Aaron-Mok/StereoCamera/CAD/Raspberry Pi HQ Camera Case - 4420496/images/back-cover.png

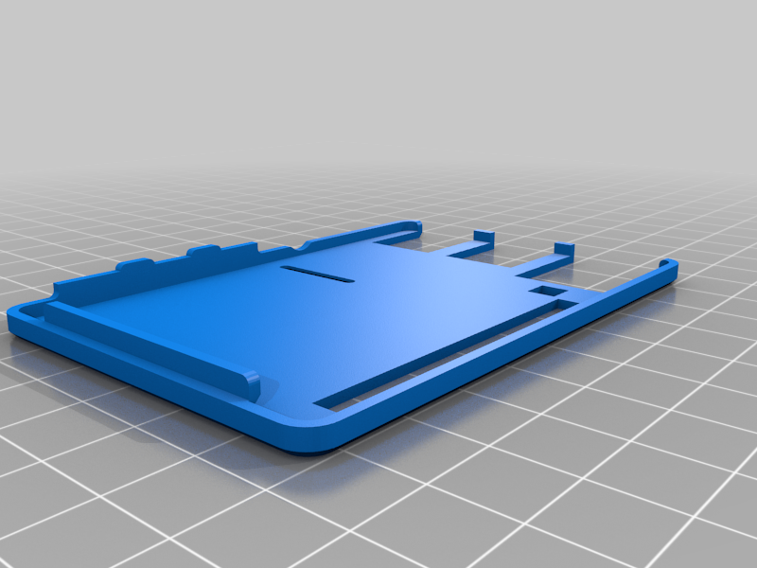
CAD/Raspberry Pi HQ Camera Case - 4420496/images/back-cover.png
