Aaron-Mok/StereoCamera/CAD/Raspberry Pi HQ Camera Case - 4420496/images/back-frame.png

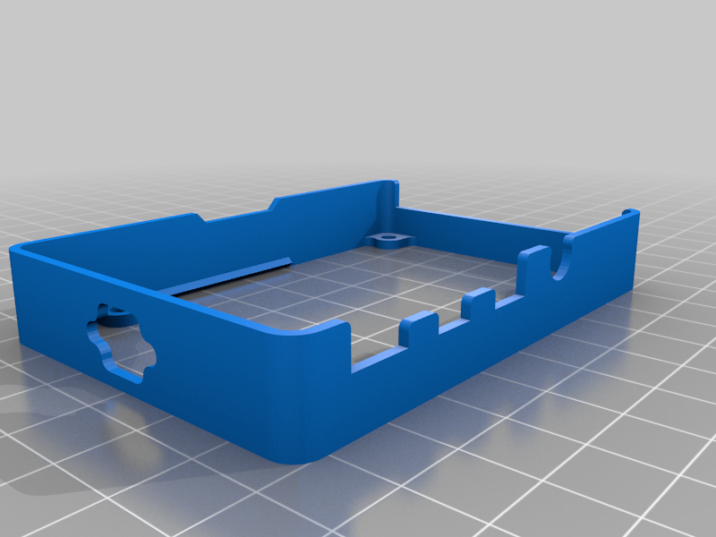
CAD/Raspberry Pi HQ Camera Case - 4420496/images/back-frame.png
