Aaron-Mok/StereoCamera/CAD/Raspberry Pi HQ Camera Case - 4420496/images/hero-camera.jpg

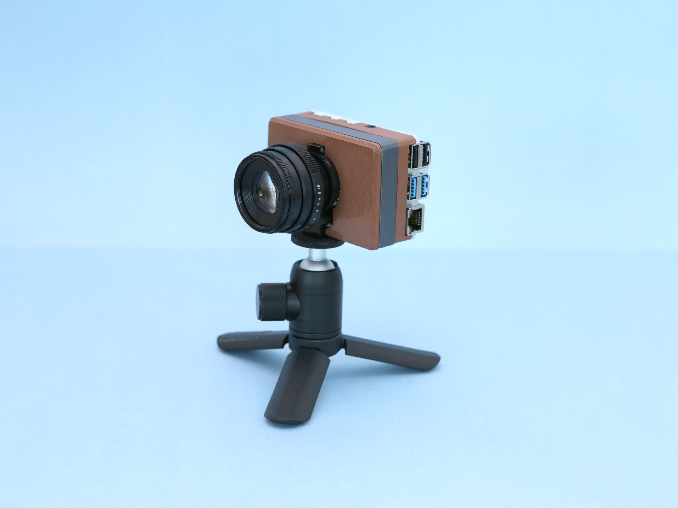
CAD/Raspberry Pi HQ Camera Case - 4420496/images/hero-camera.jpg
