Aaron-Mok/StereoCamera/CAD/Raspberry Pi HQ Camera Case - 4420496/images/pcb-mount.png

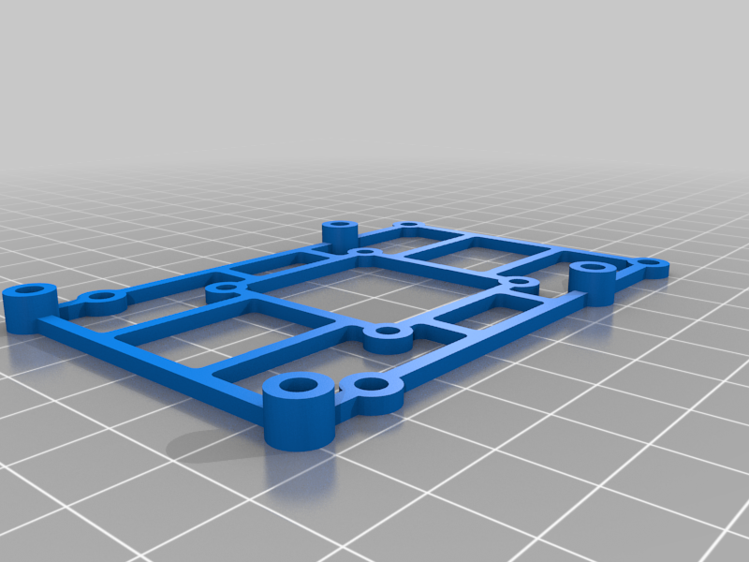
CAD/Raspberry Pi HQ Camera Case - 4420496/images/pcb-mount.png
