Aaron-Mok/StereoCamera/captures/bgr_image_awb_gamma_u801.png

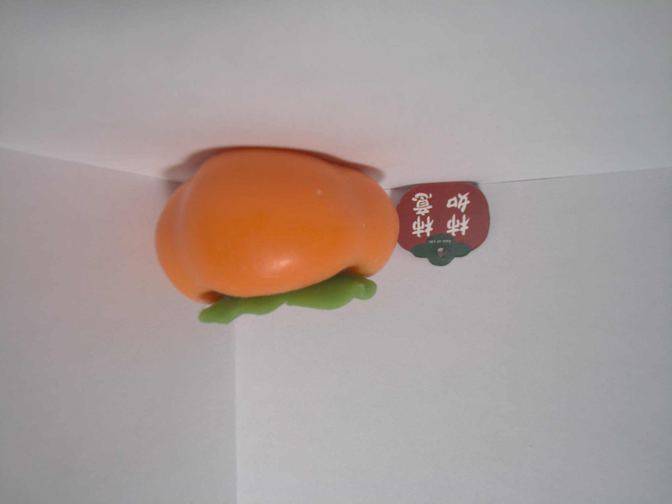
captures/bgr_image_awb_gamma_u801.png
