Aaron-Mok/StereoCamera/captures/depth_1781497462187.png

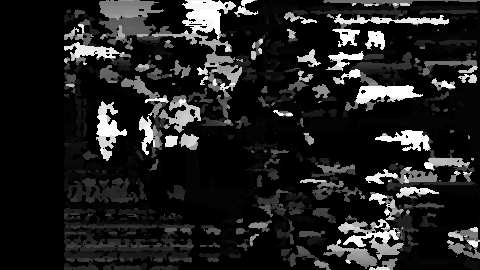
captures/depth_1781497462187.png
