Aaron-Mok/StereoCamera/captures/depth_1781998878519.png

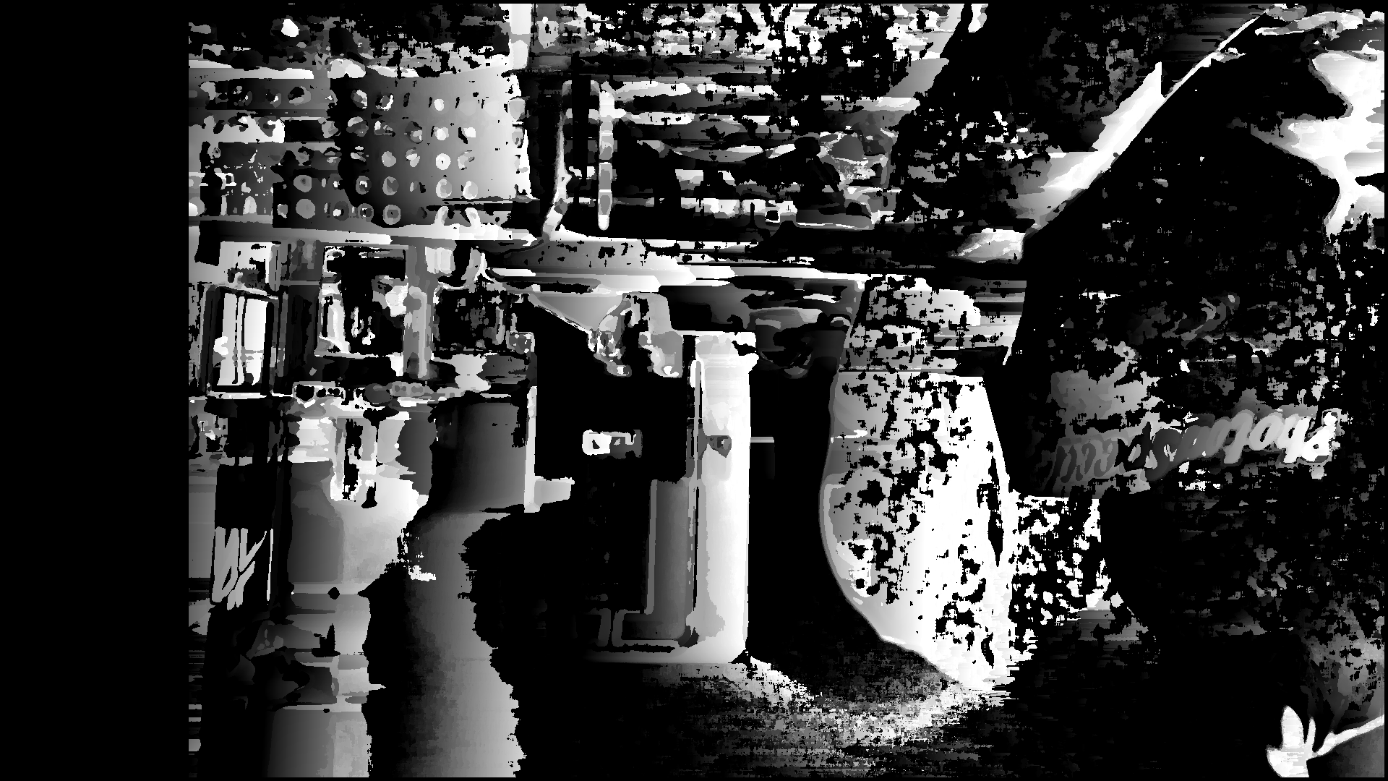
captures/depth_1781998878519.png
