Aaron-Mok/StereoCamera/captures/raw_u16_01.png

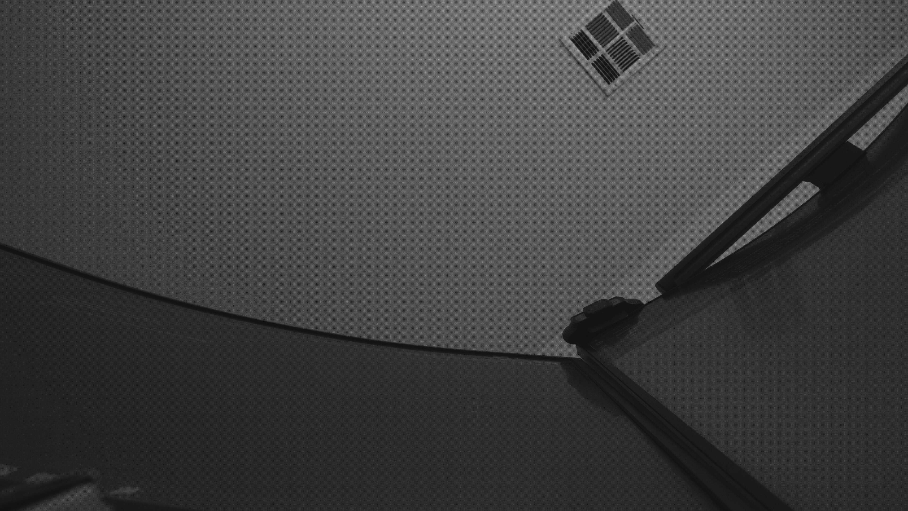
captures/raw_u16_01.png
