Aaron-Mok/StereoCamera/captures/rectL_1781497462187.png

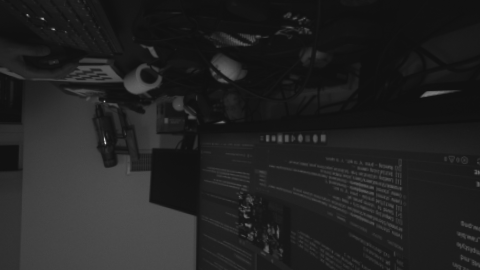
captures/rectL_1781497462187.png
