Aaron-Mok/StereoCamera/captures/rectL_1781998878519.png

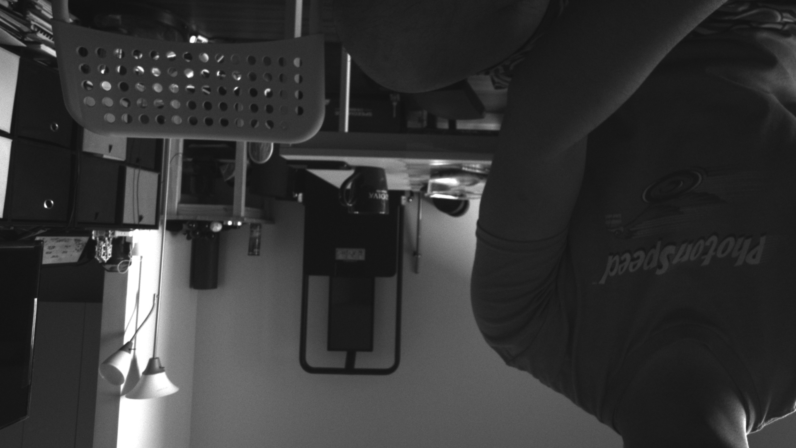
captures/rectL_1781998878519.png
