Aaron-Mok/StereoCamera/captures/rectR_1781497462187.png

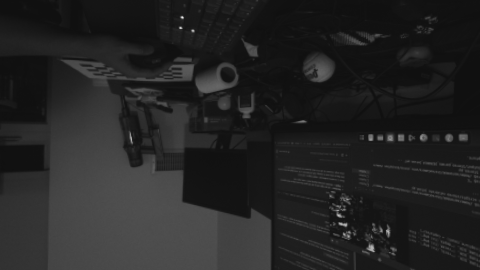
captures/rectR_1781497462187.png
