Aaron-Mok/StereoCamera/captures/rectR_1781998878519.png

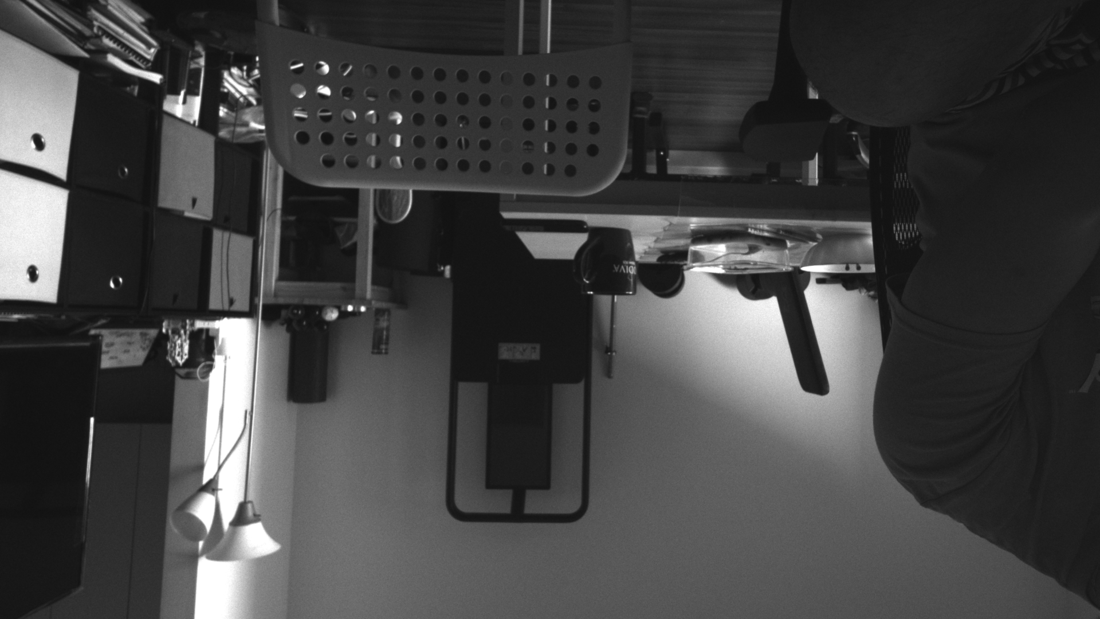
captures/rectR_1781998878519.png
