Aaron-Mok/StereoCamera/captures/white_balanced_image.png

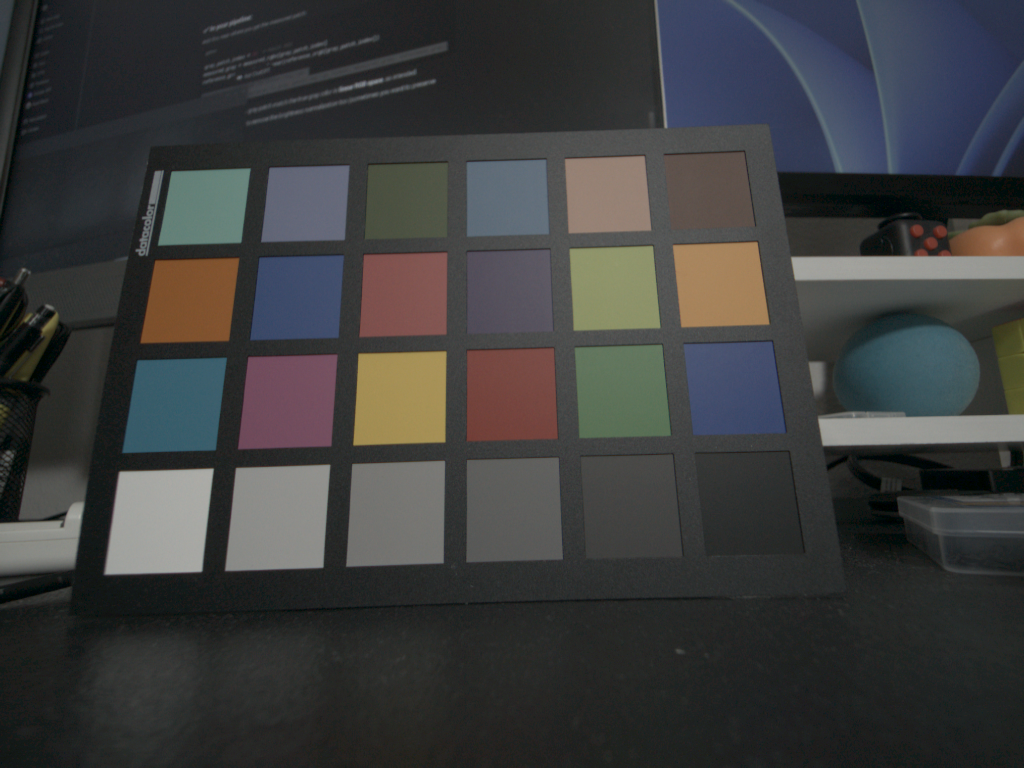
captures/white_balanced_image.png
