Aaron-Mok/StereoCamera/stereo_calib_pairs/left_1781990944117.png

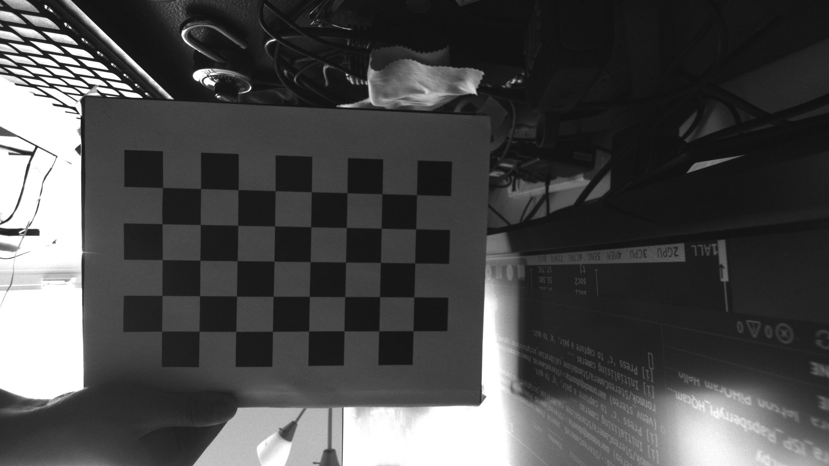
stereo_calib_pairs/left_1781990944117.png
