Aaron-Mok/StereoCamera/stereo_calib_pairs/left_1781990951715.png

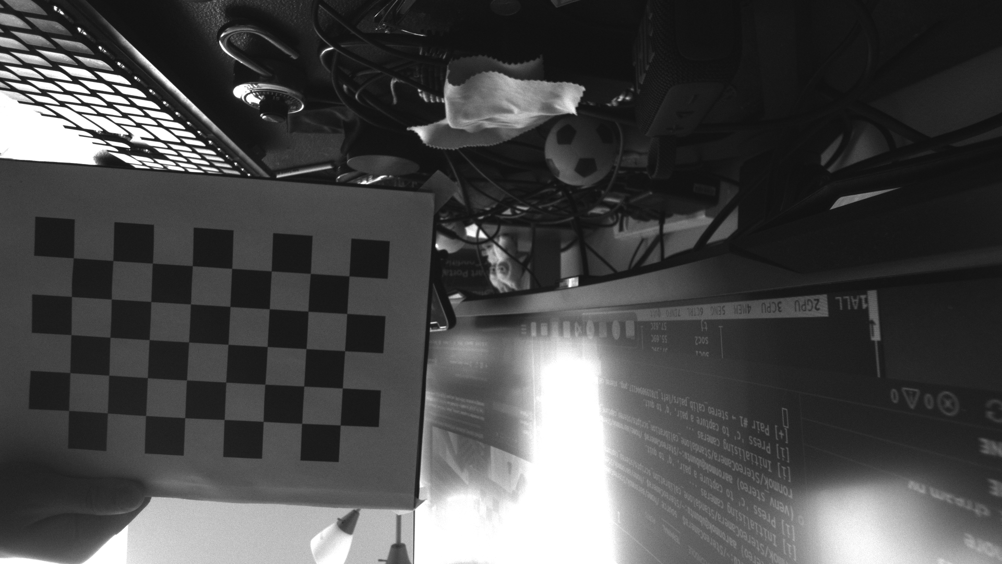
stereo_calib_pairs/left_1781990951715.png
