Aaron-Mok/StereoCamera/stereo_calib_pairs/left_1781990956050.png

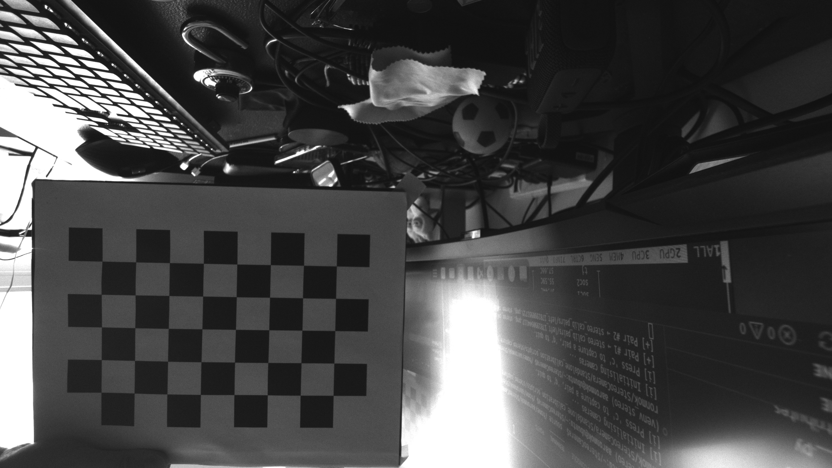
stereo_calib_pairs/left_1781990956050.png
