Aaron-Mok/StereoCamera/stereo_calib_pairs/left_1781990961881.png

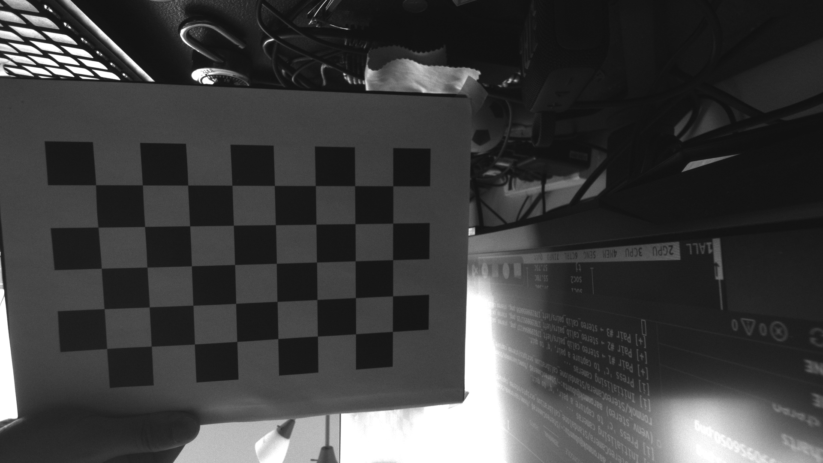
stereo_calib_pairs/left_1781990961881.png
