Aaron-Mok/StereoCamera/stereo_calib_pairs/left_1781990971266.png

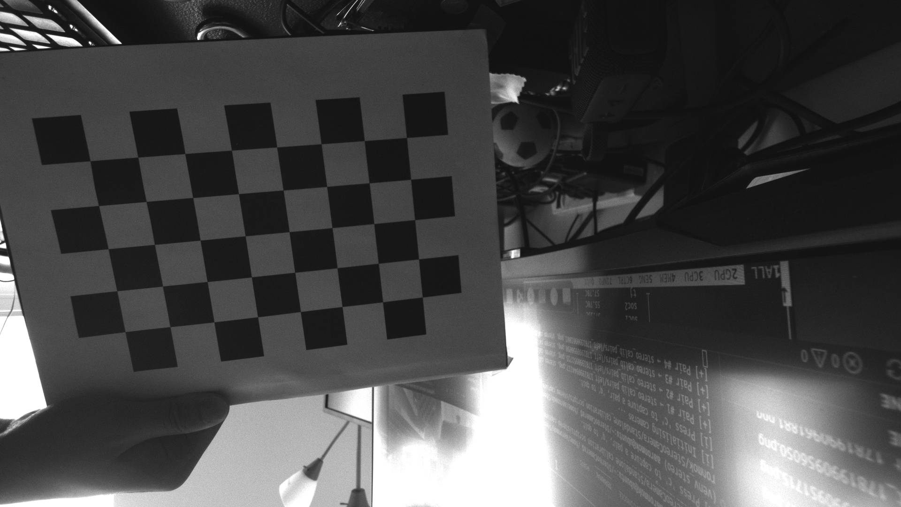
stereo_calib_pairs/left_1781990971266.png
