Aaron-Mok/StereoCamera/stereo_calib_pairs/left_1781990977469.png

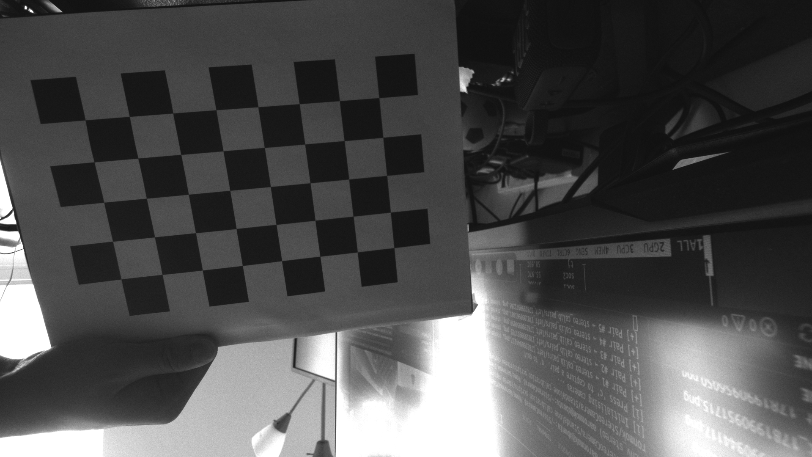
stereo_calib_pairs/left_1781990977469.png
