Aaron-Mok/StereoCamera/stereo_calib_pairs/left_1781991415851.png

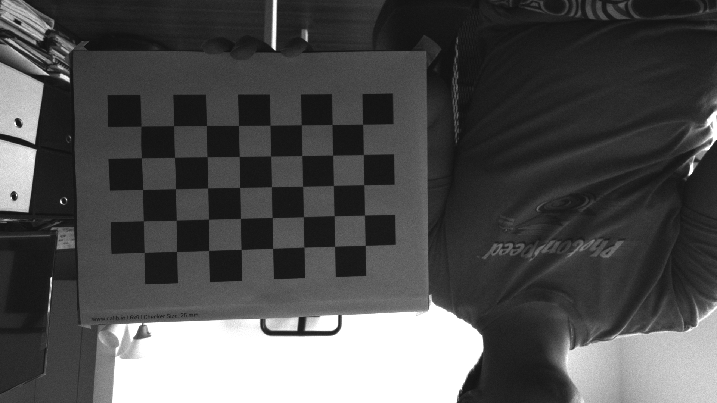
stereo_calib_pairs/left_1781991415851.png
