Aaron-Mok/StereoCamera/stereo_calib_pairs/left_1781996202573.png

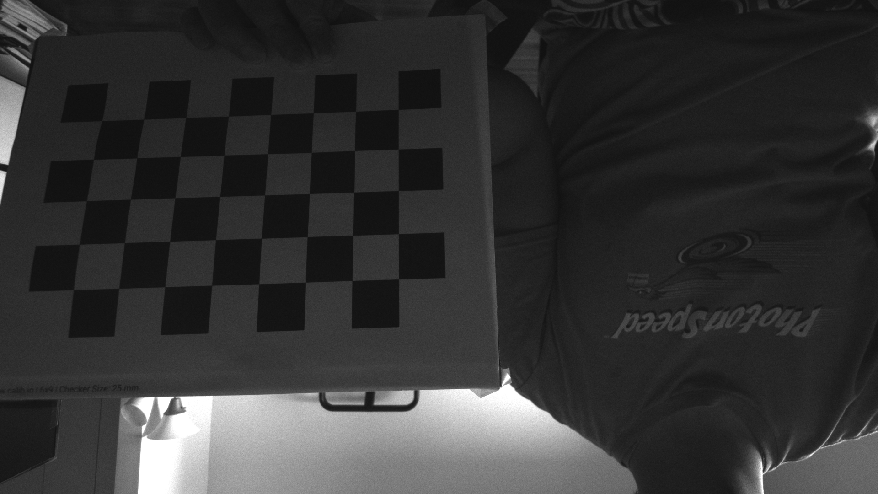
stereo_calib_pairs/left_1781996202573.png
