Aaron-Mok/StereoCamera/stereo_calib_pairs/left_1781996810830.png

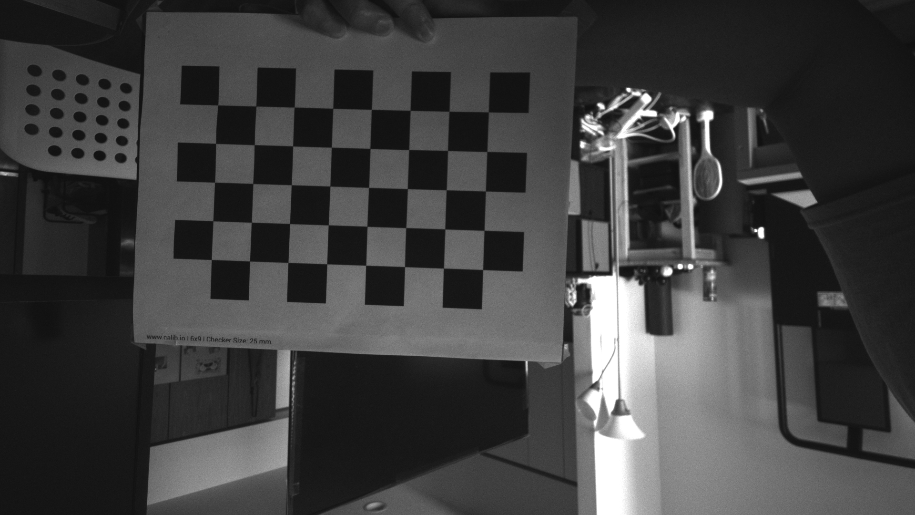
stereo_calib_pairs/left_1781996810830.png
