Aaron-Mok/StereoCamera/stereo_calib_pairs/left_1781996816100.png

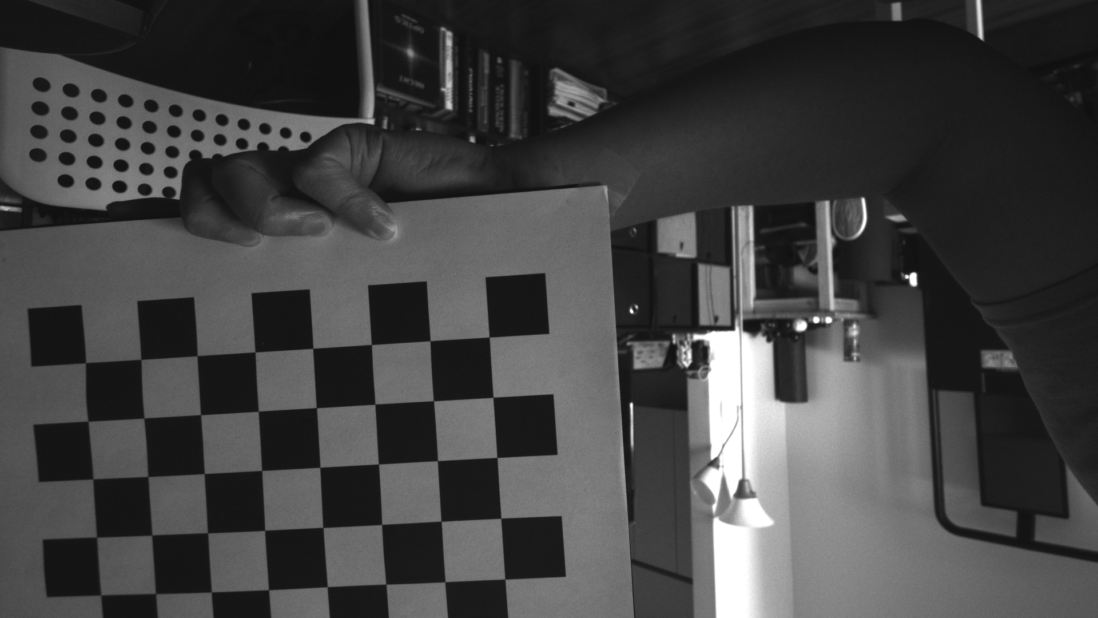
stereo_calib_pairs/left_1781996816100.png
