Aaron-Mok/StereoCamera/stereo_calib_pairs/left_1781996898139.png

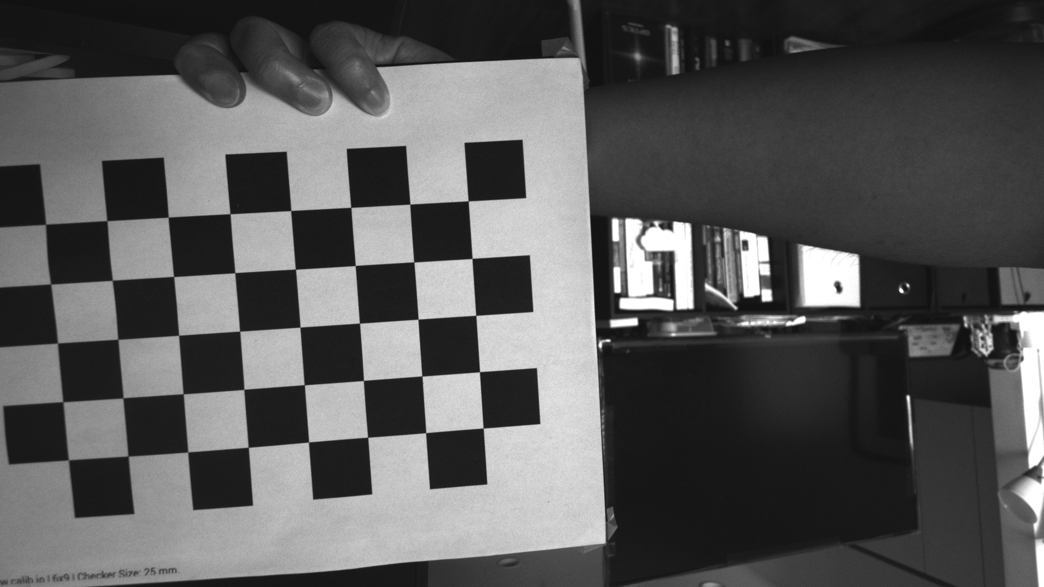
stereo_calib_pairs/left_1781996898139.png
