Aaron-Mok/StereoCamera/stereo_calib_pairs/left_1781996904151.png

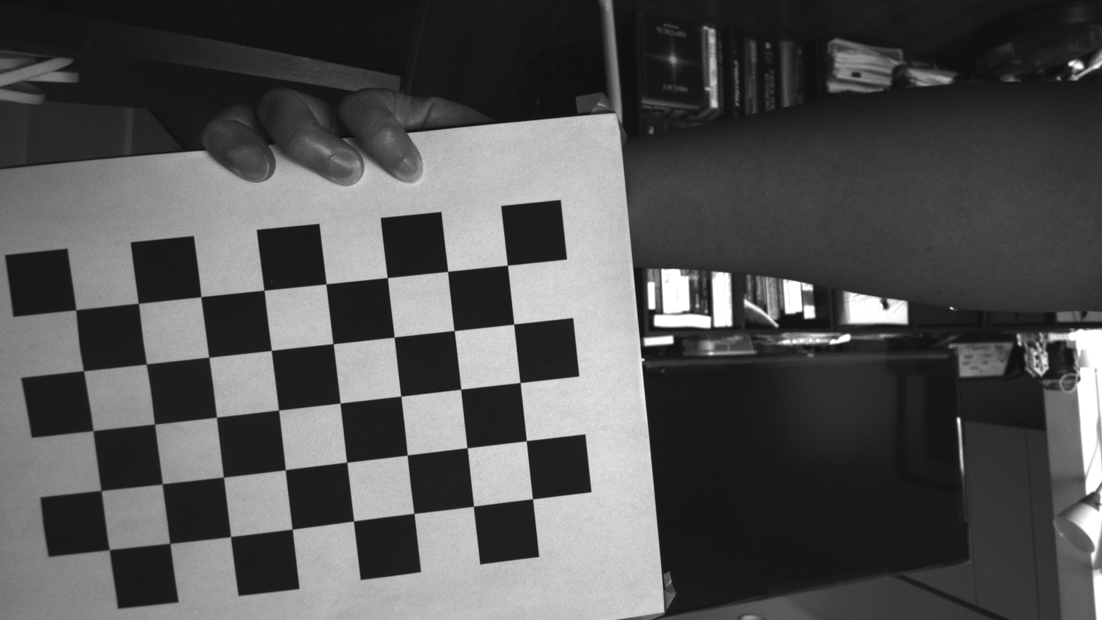
stereo_calib_pairs/left_1781996904151.png
