Aaron-Mok/StereoCamera/stereo_calib_pairs/left_1781996920679.png

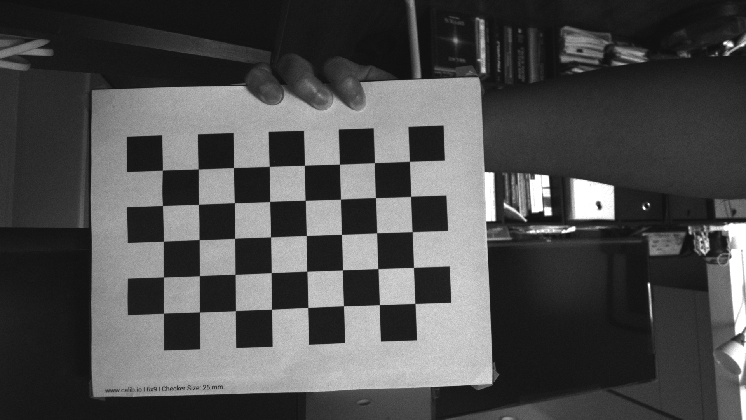
stereo_calib_pairs/left_1781996920679.png
