Aaron-Mok/StereoCamera/stereo_calib_pairs/left_1781996940578.png

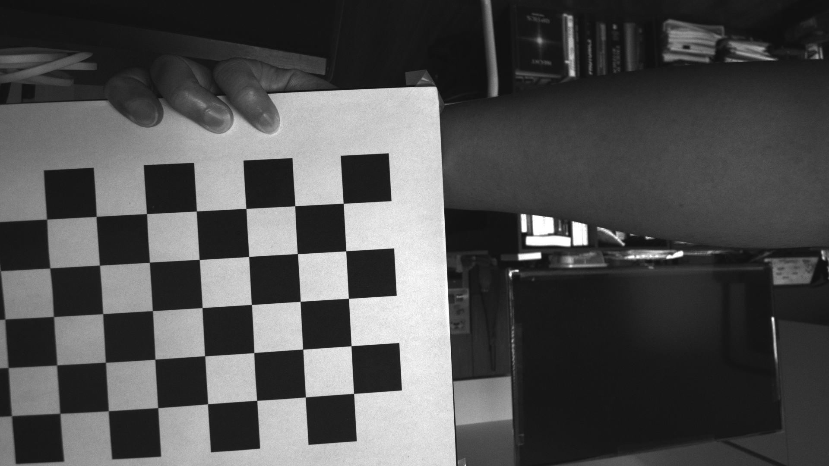
stereo_calib_pairs/left_1781996940578.png
