Aaron-Mok/StereoCamera/stereo_calib_pairs/right_1781990944117.png

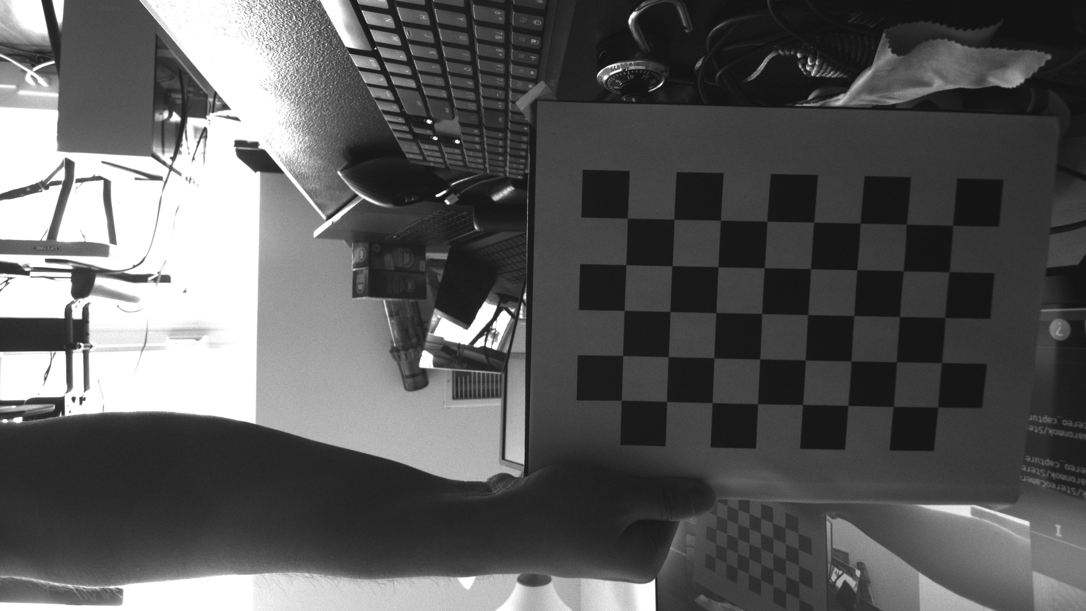
stereo_calib_pairs/right_1781990944117.png
