Aaron-Mok/StereoCamera/stereo_calib_pairs/right_1781990956050.png

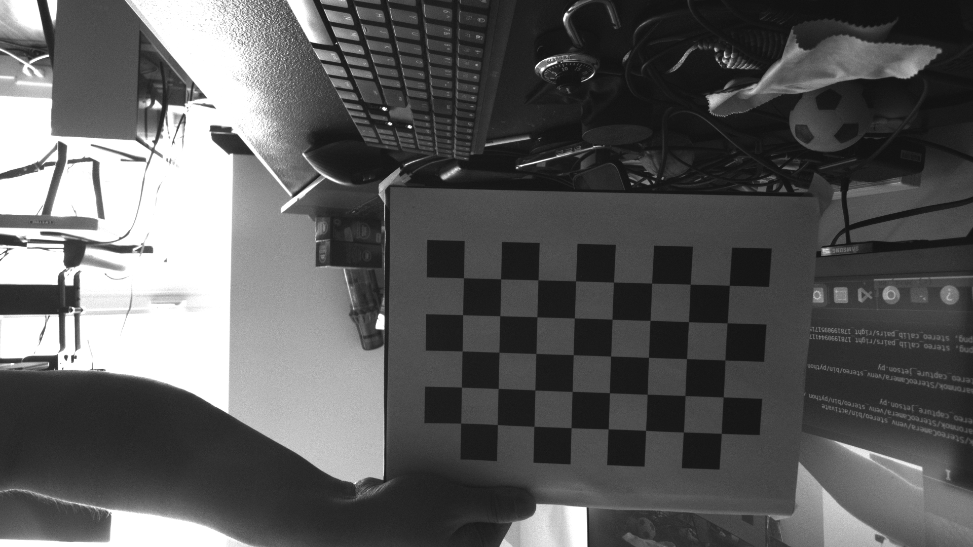
stereo_calib_pairs/right_1781990956050.png
