Aaron-Mok/StereoCamera/stereo_calib_pairs/right_1781990961881.png

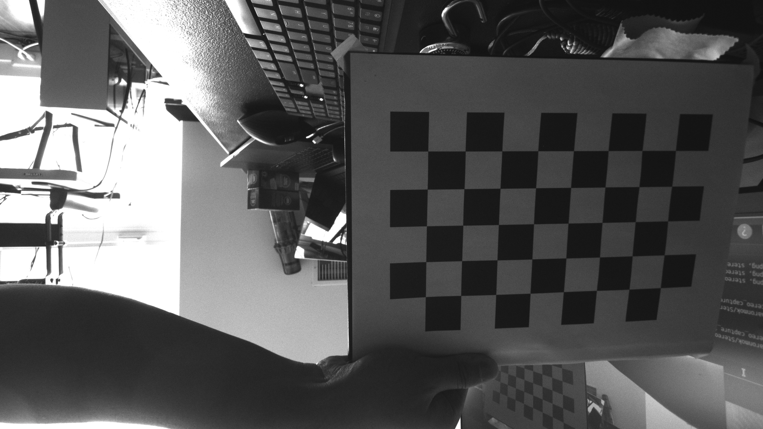
stereo_calib_pairs/right_1781990961881.png
