Aaron-Mok/StereoCamera/stereo_calib_pairs/right_1781990977469.png

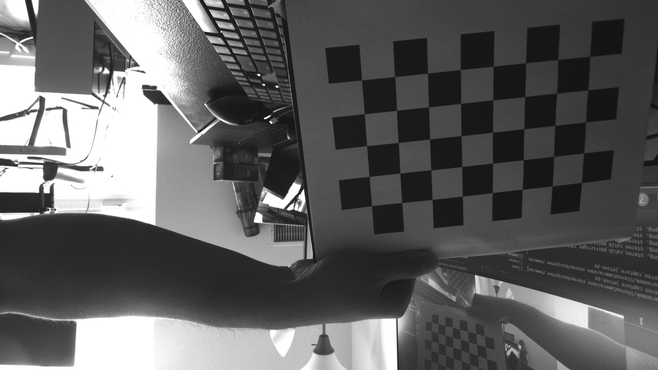
stereo_calib_pairs/right_1781990977469.png
