Aaron-Mok/StereoCamera/stereo_calib_pairs/right_1781996202573.png

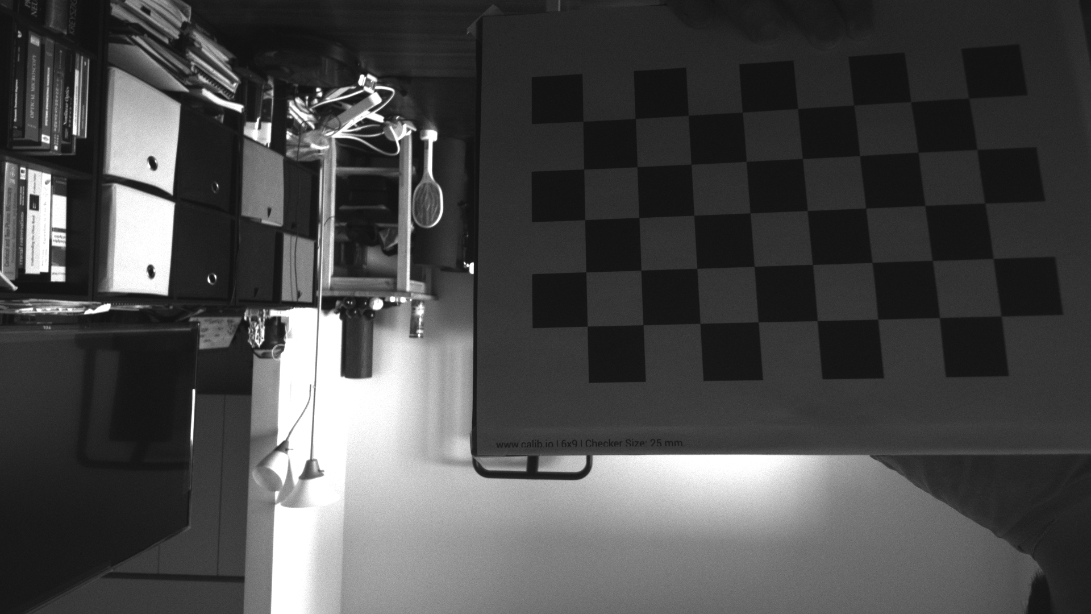
stereo_calib_pairs/right_1781996202573.png
