Aaron-Mok/StereoCamera/stereo_calib_pairs/right_1781996804988.png

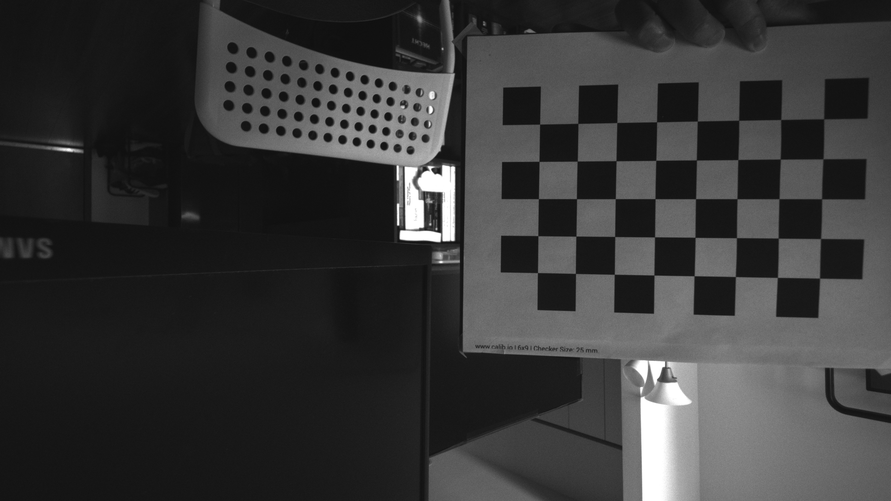
stereo_calib_pairs/right_1781996804988.png
