Aaron-Mok/StereoCamera/stereo_calib_pairs/right_1781996810830.png

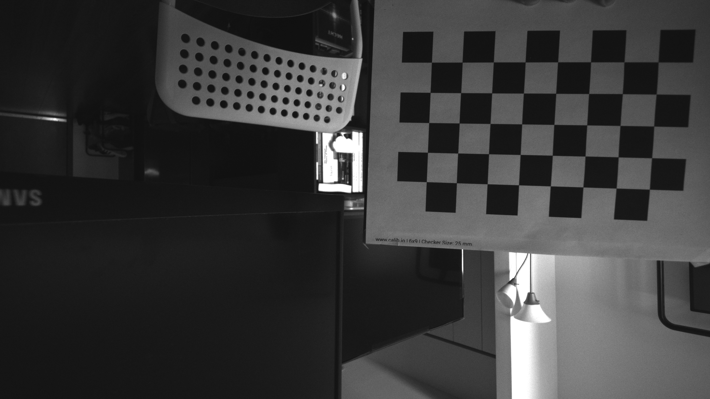
stereo_calib_pairs/right_1781996810830.png
