Aaron-Mok/StereoCamera/stereo_calib_pairs/right_1781996816100.png

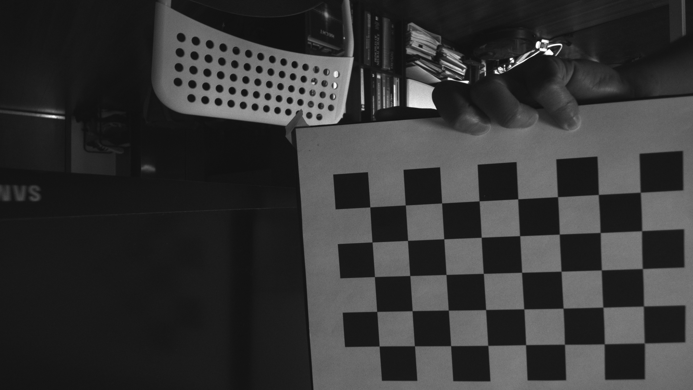
stereo_calib_pairs/right_1781996816100.png
