Aaron-Mok/StereoCamera/stereo_calib_pairs/right_1781996898139.png

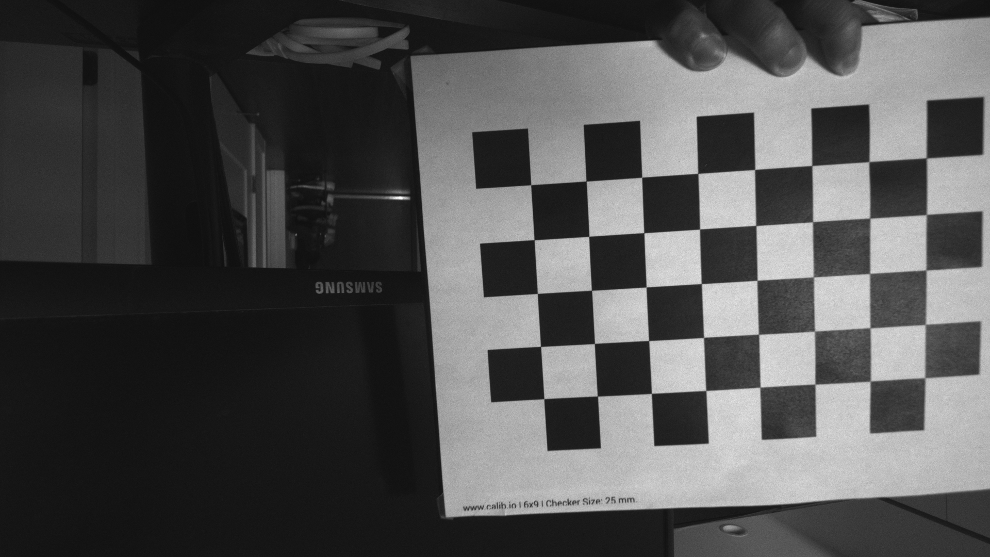
stereo_calib_pairs/right_1781996898139.png
