Aaron-Mok/StereoCamera/stereo_calib_pairs/right_1781996904151.png

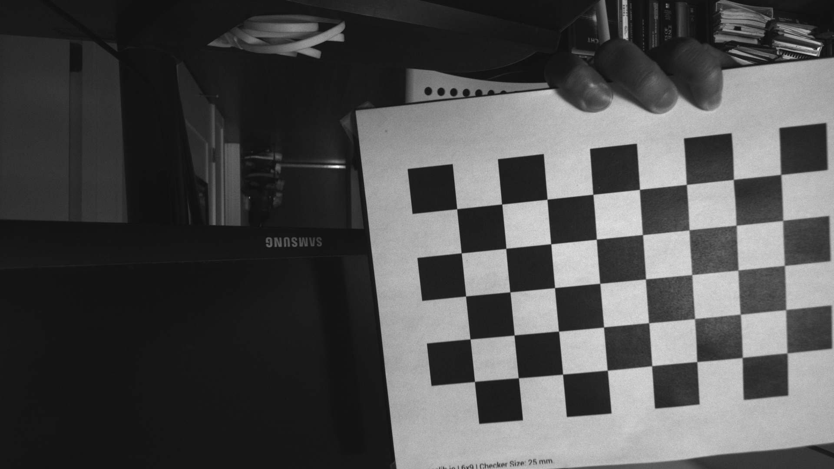
stereo_calib_pairs/right_1781996904151.png
