Aaron-Mok/StereoCamera/stereo_calib_pairs/right_1781996910558.png

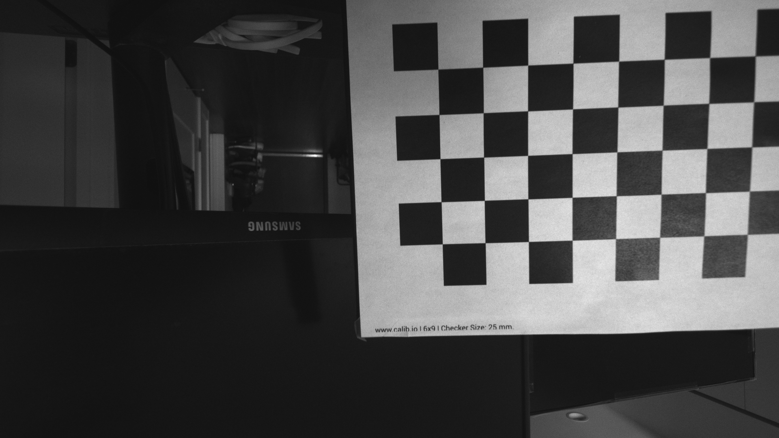
stereo_calib_pairs/right_1781996910558.png
