Aaron-Mok/StereoCamera/stereo_calib_pairs/right_1781996920679.png

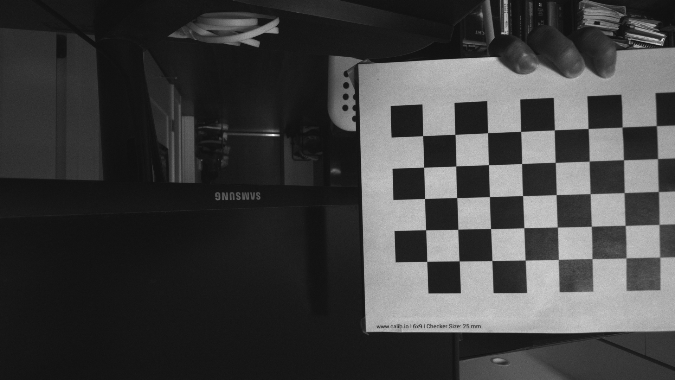
stereo_calib_pairs/right_1781996920679.png
