Aaron-Mok/StereoCamera/stereo_calib_pairs/right_1781996940578.png

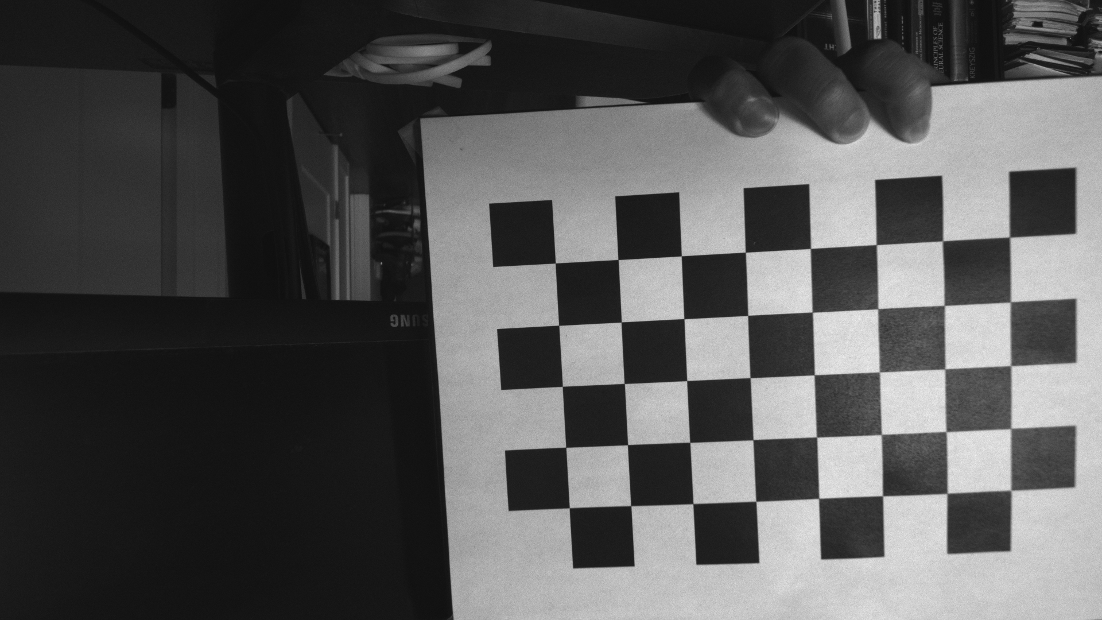
stereo_calib_pairs/right_1781996940578.png
