Aaron-Mok/StereoCamera/window.png

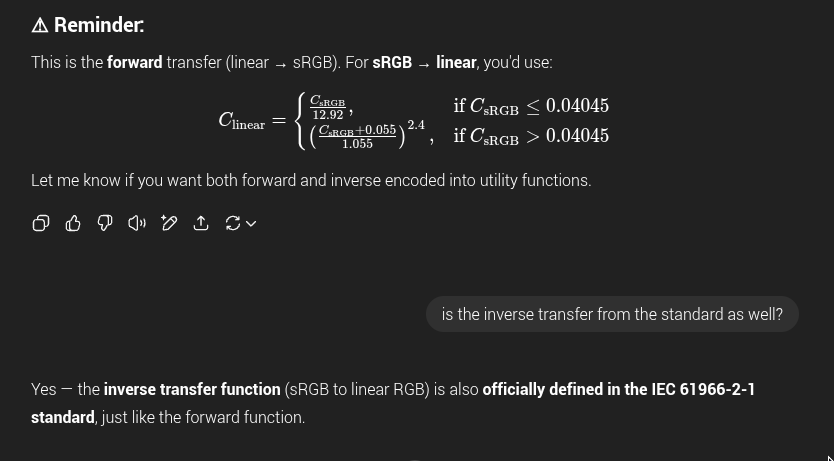
window.png
