Aaron-Mok/StereoCamera/Calibration_output/black_offset_script_check_lens_cover_open.png

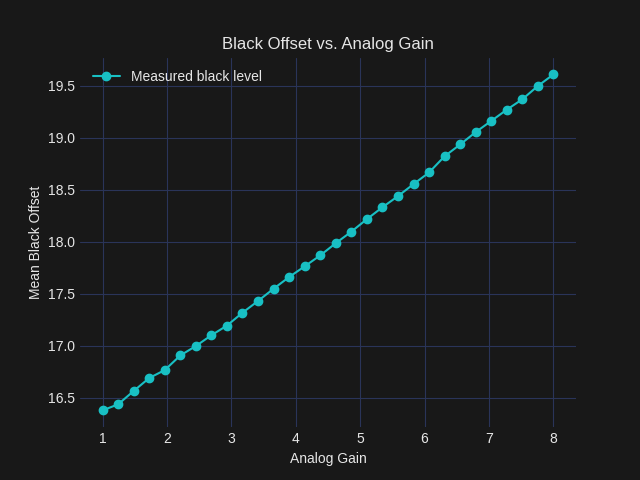
Calibration_output/black_offset_script_check_lens_cover_open.png
