Aaron-Mok/StereoCamera/stereo_calib_pairs/debug_corners/pair015_L.jpg

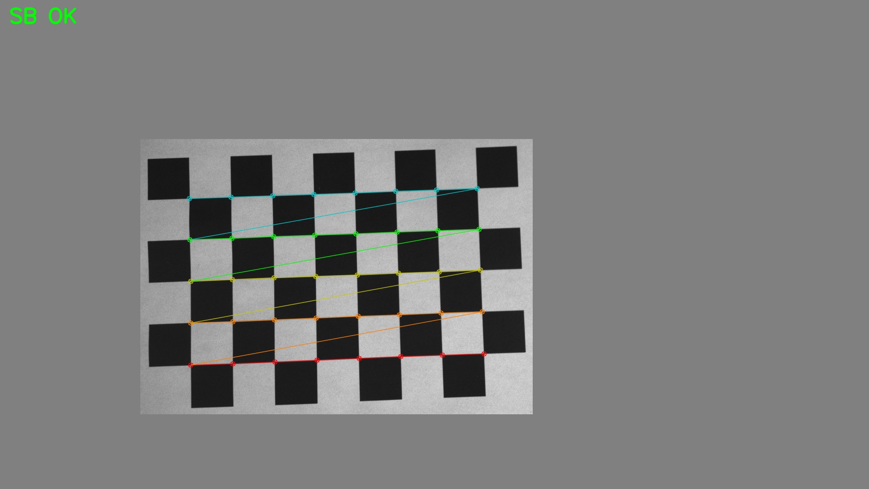
stereo_calib_pairs/debug_corners/pair015_L.jpg
