Aaron-Mok/StereoCamera/stereo_calib_pairs/debug_corners/pair016_L.jpg

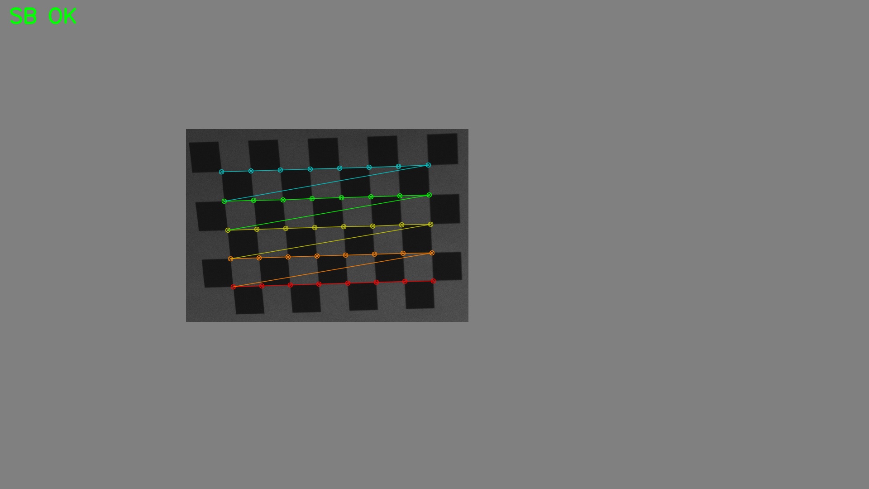
stereo_calib_pairs/debug_corners/pair016_L.jpg
