Aaron-Mok/StereoCamera/stereo_calib_pairs/debug_corners/pair018_L.jpg

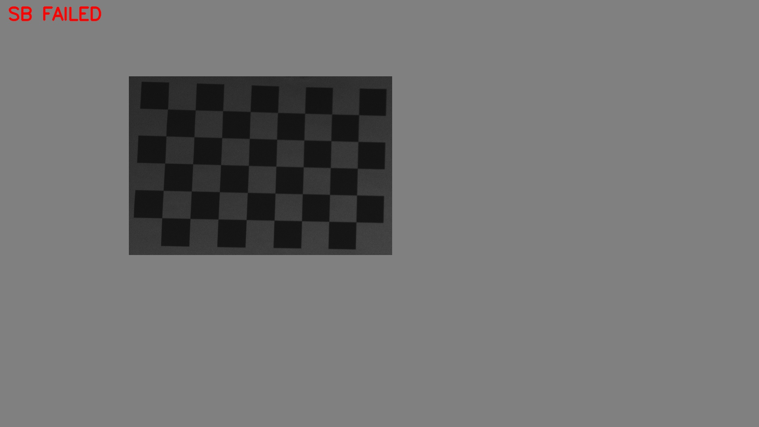
stereo_calib_pairs/debug_corners/pair018_L.jpg
