Aaron-Mok/StereoCamera/stereo_calib_pairs/debug_corners/pair019_R.jpg

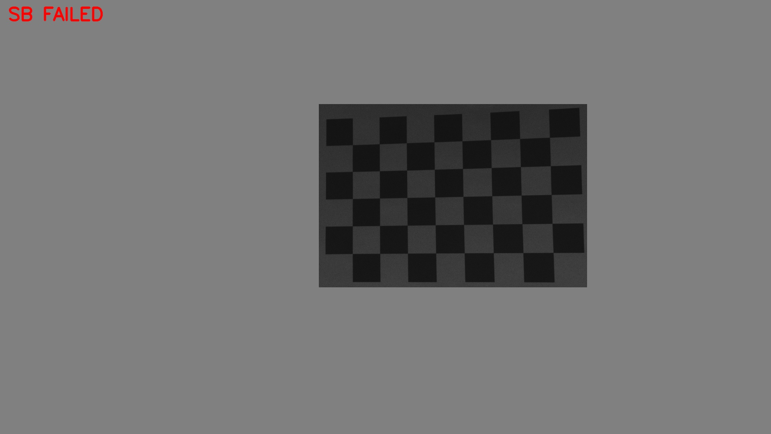
stereo_calib_pairs/debug_corners/pair019_R.jpg
