Aaron-Mok/StereoCamera/argus_stream.py

import cv2
import sys

def gstreamer_pipeline(width=1920, height=1080, fps=30, flip=0):
    return (
        f"nvarguscamerasrc ! "
        f"video/x-raw(memory:NVMM), width={width}, height={height}, framerate={fps}/1 ! "
        f"nvvidconv flip-method={flip} ! "
        f"video/x-raw, format=BGRx ! "
        f"videoconvert ! "
        f"video/x-raw, format=BGR ! "
        f"appsink drop=1"
    )

pipeline = gstreamer_pipeline()
print(f"Pipeline: {pipeline}")

cap = cv2.VideoCapture(pipeline, cv2.CAP_GSTREAMER)

if not cap.isOpened():
    print("ERROR: Could not open camera via nvarguscamerasrc.")
    print("Check that the Argus daemon is running and the camera is connected.")
    sys.exit(1)

print("Camera opened successfully. Press 'q' to quit.")

while True:
    ret, frame = cap.read()
    if not ret:
        print("ERROR: Failed to grab frame.")
        break

    h, w = frame.shape[:2]
    cv2.putText(frame, f"{w}x{h}", (20, 40), cv2.FONT_HERSHEY_SIMPLEX, 1, (0, 255, 0), 2)
    cv2.imshow("Argus Stream", frame)

    if cv2.waitKey(1) & 0xFF == ord('q'):
        break

cap.release()
cv2.destroyAllWindows()
