Aaron-Mok/StereoCamera/Standalone_calibration_scripts/stereo_calibrate_live_jetson.py

#!/usr/bin/env python3
"""
Stereo calibration script for dual Pi HQ cameras on Jetson Nano.
Cameras are read as raw Bayer uint16 via v4l2-ctl; green channel is
extracted for calibration since it has the most pixels and sharpest detail.

Controls:
  c  - capture a pair (only works when both cameras detect the checkerboard)
  s  - run stereo calibration with collected pairs
  q  - quit without calibrating

TODO: This is trying to use findChessboardCOrnerSB, which does not seems to work.
Can switch back to findChessboardCorners if needed, but SB is supposed to be more robust and accurate. 
"""
import sys
import os
sys.path.insert(0, os.path.abspath(os.path.join(os.path.dirname(__file__), "..")))

import cv2
import numpy as np
import time

from ISP.binning import extract_green, bin_2x2
from camera_utils import initialize_camera_jetson, capture_raw_frame_jetson
from conversion_utils import bit16_to_bit8

# ─── Settings ──────────────────────────────────────────────────────────────────
LEFT_DEVICE  = "/dev/video0"
RIGHT_DEVICE = "/dev/video1"

W, H         = 3840, 2160          # sensor resolution
EXPOSURE     = 33000
GAIN         = 200
FRAME_RATE   = 30000000

# extract_green → (H//2, W//2), then bin_2x2 → (H//4, W//4) = (540, 960)
IMG_W, IMG_H = W // 4, H // 4

# Checkerboard inner-corner count (not number of squares)
CB_COLS       = 8
CB_ROWS       = 5
SQUARE_SIZE_M = 0.025              # square side length in metres

MIN_PAIRS = 15

OUT_DIR  = "stereo_calib_pairs"
YAML_OUT = "stereo_params.yml"

# ───────────────────────────────────────────────────────────────────────────────


def raw_to_gray8(raw_u16: np.ndarray) -> np.ndarray:
    """Extract green channel, 2×2 bin to 960×540, convert to uint8."""
    return bit16_to_bit8(bin_2x2(extract_green(raw_u16)))


def find_corners(gray, pattern_size):
    """Detect directly at 960×540. SB includes subpixel — no further scaling needed."""
    sb_flags = cv2.CALIB_CB_NORMALIZE_IMAGE
    return cv2.findChessboardCornersSB(gray, pattern_size, sb_flags)


def make_object_points(pattern_size, square_size_m):
    cb_cols, cb_rows = pattern_size
    objp = np.zeros((cb_rows * cb_cols, 3), np.float32)
    objp[:, :2] = np.mgrid[0:cb_cols, 0:cb_rows].T.reshape(-1, 2)
    objp *= square_size_m
    return objp


def save_yaml(filepath, data_dict):
    fs = cv2.FileStorage(filepath, cv2.FILE_STORAGE_WRITE)
    for k, v in data_dict.items():
        fs.write(k, v)
    fs.release()


def main():
    os.makedirs(OUT_DIR, exist_ok=True)

    print("[i] Initialising left camera  ...")
    pL, _ = initialize_camera_jetson(LEFT_DEVICE,  W, H, EXPOSURE, GAIN, FRAME_RATE)
    print("[i] Initialising right camera ...")
    pR, _ = initialize_camera_jetson(RIGHT_DEVICE, W, H, EXPOSURE, GAIN, FRAME_RATE)

    pattern_size = (CB_COLS, CB_ROWS)
    objp = make_object_points(pattern_size, SQUARE_SIZE_M)
    image_size   = (IMG_W, IMG_H)   # (width, height) as OpenCV expects

    objpoints  = []
    imgpointsL = []
    imgpointsR = []
    pair_count = 0

    font = cv2.FONT_HERSHEY_SIMPLEX

    print("[i] Press 'c' to capture a pair when both detections are green.")
    print(f"[i] Press 's' to run calibration (need at least {MIN_PAIRS} pairs).")
    print("[i] Press 'q' to quit.")

    while True:
        raw_L = capture_raw_frame_jetson(pL, W, H)
        raw_R = capture_raw_frame_jetson(pR, W, H)
        if raw_L is None or raw_R is None:
            print("[!] Frame grab failed — exiting.")
            break

        grayL = raw_to_gray8(raw_L)
        grayR = raw_to_gray8(raw_R)

        foundL, cornersL = find_corners(grayL, pattern_size)
        foundR, cornersR = find_corners(grayR, pattern_size)

        # 960×540 is directly displayable — no resize needed
        showL = grayL.copy()
        showR = grayR.copy()

        if foundL:
            cv2.drawChessboardCorners(showL, pattern_size, cornersL, foundL)
        if foundR:
            cv2.drawChessboardCorners(showR, pattern_size, cornersR, foundR)

        colorL = (0, 200, 0) if foundL else (0, 0, 255)
        colorR = (0, 200, 0) if foundR else (0, 0, 255)
        cv2.putText(showL, f"Left:  {'OK' if foundL else 'NO'}",  (20, 40),  font, 1.0, colorL, 2, cv2.LINE_AA)
        cv2.putText(showR, f"Right: {'OK' if foundR else 'NO'}", (20, 40),  font, 1.0, colorR, 2, cv2.LINE_AA)
        cv2.putText(showL, f"Pairs: {pair_count}",               (20, 80),  font, 0.8, (255, 255, 255), 2, cv2.LINE_AA)
        cv2.putText(showR, f"c=capture  s=calibrate  q=quit",    (20, 80),  font, 0.8, (255, 255, 255), 2, cv2.LINE_AA)

        cv2.imshow("Left", showL)
        cv2.imshow("Right", showR)

        key = cv2.waitKey(1) & 0xFF

        if key == ord('q'):
            print("[i] Quit — no calibration saved.")
            break

        elif key == ord('c'):
            if foundL and foundR:
                ts = int(time.time() * 1000)
                lp = os.path.join(OUT_DIR, f"left_{ts}.png")
                rp = os.path.join(OUT_DIR, f"right_{ts}.png")
                cv2.imwrite(lp, grayL)
                cv2.imwrite(rp, grayR)
                objpoints.append(objp.copy())
                imgpointsL.append(cornersL)
                imgpointsR.append(cornersR)
                pair_count += 1
                print(f"[+] Pair #{pair_count} saved → {lp}, {rp}")
            else:
                print("[!] Skipped — need checkerboard visible in BOTH cameras.")

        elif key == ord('s'):
            if pair_count < MIN_PAIRS:
                print(f"[!] Need at least {MIN_PAIRS} pairs; have {pair_count}.")
                continue

            print("[i] Running per-camera calibration ...")
            retL, K1, D1, _, _ = cv2.calibrateCamera(objpoints, imgpointsL, image_size, None, None)
            retR, K2, D2, _, _ = cv2.calibrateCamera(objpoints, imgpointsR, image_size, None, None)
            print(f"[i] RMS  left={retL:.4f}  right={retR:.4f}")

            sc_flags = (cv2.CALIB_USE_INTRINSIC_GUESS |
                        cv2.CALIB_RATIONAL_MODEL       |
                        cv2.CALIB_FIX_K3)
            if hasattr(cv2, "CALIB_FIX_TAUX_TAUY"):
                sc_flags |= cv2.CALIB_FIX_TAUX_TAUY

            sc_criteria = (cv2.TERM_CRITERIA_MAX_ITER + cv2.TERM_CRITERIA_EPS, 100, 1e-6)

            print("[i] Running stereoCalibrate ...")
            rms, K1, D1, K2, D2, R, T, E, F = cv2.stereoCalibrate(
                objpoints, imgpointsL, imgpointsR,
                K1, D1, K2, D2,
                image_size, criteria=sc_criteria, flags=sc_flags
            )
            print(f"[i] Stereo RMS : {rms:.4f}")
            print(f"[i] Baseline   : {np.linalg.norm(T)*100:.2f} cm")

            print("[i] Computing stereoRectify + remap tables ...")
            R1, R2, P1, P2, Q, roi1, roi2 = cv2.stereoRectify(
                K1, D1, K2, D2, image_size, R, T,
                flags=cv2.CALIB_ZERO_DISPARITY, alpha=0
            )
            map1x, map1y = cv2.initUndistortRectifyMap(K1, D1, R1, P1, image_size, cv2.CV_32FC1)
            map2x, map2y = cv2.initUndistortRectifyMap(K2, D2, R2, P2, image_size, cv2.CV_32FC1)

            out = {
                "image_width":  image_size[0],
                "image_height": image_size[1],
                "K1": K1, "D1": D1,
                "K2": K2, "D2": D2,
                "R":  R,  "T":  T,  "E": E, "F": F,
                "R1": R1, "R2": R2, "P1": P1, "P2": P2, "Q": Q,
                "roi1": np.array(roi1, dtype=np.int32),
                "roi2": np.array(roi2, dtype=np.int32),
                "map1x": map1x, "map1y": map1y,
                "map2x": map2x, "map2y": map2y,
                "square_size_m": float(SQUARE_SIZE_M),
                "cb_cols": int(CB_COLS),
                "cb_rows": int(CB_ROWS),
            }
            save_yaml(YAML_OUT, out)
            print(f"[✓] Saved to '{YAML_OUT}'")

            # ── Rectified live preview ──────────────────────────────────────
            print("[i] Rectified preview — press 'q' to exit.")
            gpu_map1x = cv2.cuda_GpuMat(); gpu_map1x.upload(map1x)
            gpu_map1y = cv2.cuda_GpuMat(); gpu_map1y.upload(map1y)
            gpu_map2x = cv2.cuda_GpuMat(); gpu_map2x.upload(map2x)
            gpu_map2y = cv2.cuda_GpuMat(); gpu_map2y.upload(map2y)

            while True:
                raw_L2 = capture_raw_frame_jetson(pL, W, H)
                raw_R2 = capture_raw_frame_jetson(pR, W, H)
                if raw_L2 is None or raw_R2 is None:
                    break
                gL2 = raw_to_gray8(raw_L2)
                gR2 = raw_to_gray8(raw_R2)

                gpu_gL2 = cv2.cuda_GpuMat(); gpu_gL2.upload(gL2)
                gpu_gR2 = cv2.cuda_GpuMat(); gpu_gR2.upload(gR2)
                gpu_rectL = cv2.cuda.remap(gpu_gL2, gpu_map1x, gpu_map1y, cv2.INTER_LINEAR)
                gpu_rectR = cv2.cuda.remap(gpu_gR2, gpu_map2x, gpu_map2y, cv2.INTER_LINEAR)

                # Resize to 960×540 on GPU, cvtColor, download for hconcat
                # 960×540 frames — cvtColor on GPU, hconcat on CPU → 1920×540
                bgrL = cv2.cuda.cvtColor(gpu_rectL, cv2.COLOR_GRAY2BGR).download()
                bgrR = cv2.cuda.cvtColor(gpu_rectR, cv2.COLOR_GRAY2BGR).download()
                both = cv2.hconcat([bgrL, bgrR])  # 1920×540 — directly displayable
                for y in range(0, both.shape[0], 60):
                    cv2.line(both, (0, y), (both.shape[1] - 1, y), (0, 255, 0), 1, cv2.LINE_AA)
                cv2.imshow("Rectified Preview (q to quit)", both)
                if cv2.waitKey(1) & 0xFF == ord('q'):
                    break
            break

    cv2.destroyAllWindows()
    pL.terminate()
    pR.terminate()


if __name__ == "__main__":
    main()
