Aaron-Mok/StereoCamera/Standalone_calibration_scripts/stereo_capture_jetson.py

#!/usr/bin/env python3
"""
Capture stereo image pairs for offline calibration.
Live preview at 960×540 for framing; saves full 1920×1080 green-channel images.

Controls:
  c - capture a pair
  q - quit
"""
import sys
import os
sys.path.insert(0, os.path.abspath(os.path.join(os.path.dirname(__file__), "..")))

import cv2
import numpy as np
import time

from ISP.binning import extract_green
from camera_utils import initialize_camera_jetson, capture_raw_frame_jetson
from conversion_utils import bit16_to_bit8

# ─── Settings ──────────────────────────────────────────────────────────────────
LEFT_DEVICE  = "/dev/video0"
RIGHT_DEVICE = "/dev/video1"

W, H       = 3840, 2160
EXPOSURE   = 33000
GAIN       = 200
FRAME_RATE = 30000000

OUT_DIR = "stereo_calib_pairs"
# ───────────────────────────────────────────────────────────────────────────────


def main():
    os.makedirs(OUT_DIR, exist_ok=True)

    print("[i] Initialising cameras ...")
    pL, _ = initialize_camera_jetson(LEFT_DEVICE,  W, H, EXPOSURE, GAIN, FRAME_RATE)
    pR, _ = initialize_camera_jetson(RIGHT_DEVICE, W, H, EXPOSURE, GAIN, FRAME_RATE)

    print("[i] Press 'c' to capture a pair, 'q' to quit.")
    pair_count = 0
    font = cv2.FONT_HERSHEY_SIMPLEX

    while True:
        raw_L = capture_raw_frame_jetson(pL, W, H)
        raw_R = capture_raw_frame_jetson(pR, W, H)
        if raw_L is None or raw_R is None:
            print("[!] Frame grab failed.")
            break

        # Full 1920×1080 green channel — saved on capture
        greenL = bit16_to_bit8(extract_green(raw_L))
        greenR = bit16_to_bit8(extract_green(raw_R))

        # Downscale to 960×540 on GPU for live preview
        gpu_L = cv2.cuda_GpuMat(); gpu_L.upload(greenL)
        gpu_R = cv2.cuda_GpuMat(); gpu_R.upload(greenR)
        prevL = cv2.cuda.resize(gpu_L, (960, 540)).download()
        prevR = cv2.cuda.resize(gpu_R, (960, 540)).download()

        cv2.putText(prevL, f"Pairs: {pair_count}", (20, 40), font, 1.0, (255, 255, 255), 2, cv2.LINE_AA)
        cv2.putText(prevL, "c=capture  q=quit",    (20, 80), font, 0.8, (200, 200, 200), 2, cv2.LINE_AA)
        cv2.imshow("Left",  prevL)
        cv2.imshow("Right", prevR)

        key = cv2.waitKey(1) & 0xFF
        if key == ord('q'):
            break
        elif key == ord('c'):
            ts = int(time.time() * 1000)
            lp = os.path.join(OUT_DIR, f"left_{ts}.png")
            rp = os.path.join(OUT_DIR, f"right_{ts}.png")
            cv2.imwrite(lp, greenL)
            cv2.imwrite(rp, greenR)
            pair_count += 1
            print(f"[+] Pair #{pair_count} → {lp}, {rp}")

    cv2.destroyAllWindows()
    pL.terminate()
    pR.terminate()


if __name__ == "__main__":
    main()
